adoble/Internet-Radio-Module/hardware/electronics/irm_pcb/irm_pcb.kicad_pcb

## KiCad design hardware/electronics/irm_pcb/irm_pcb.kicad_pcb (2019-12-27)

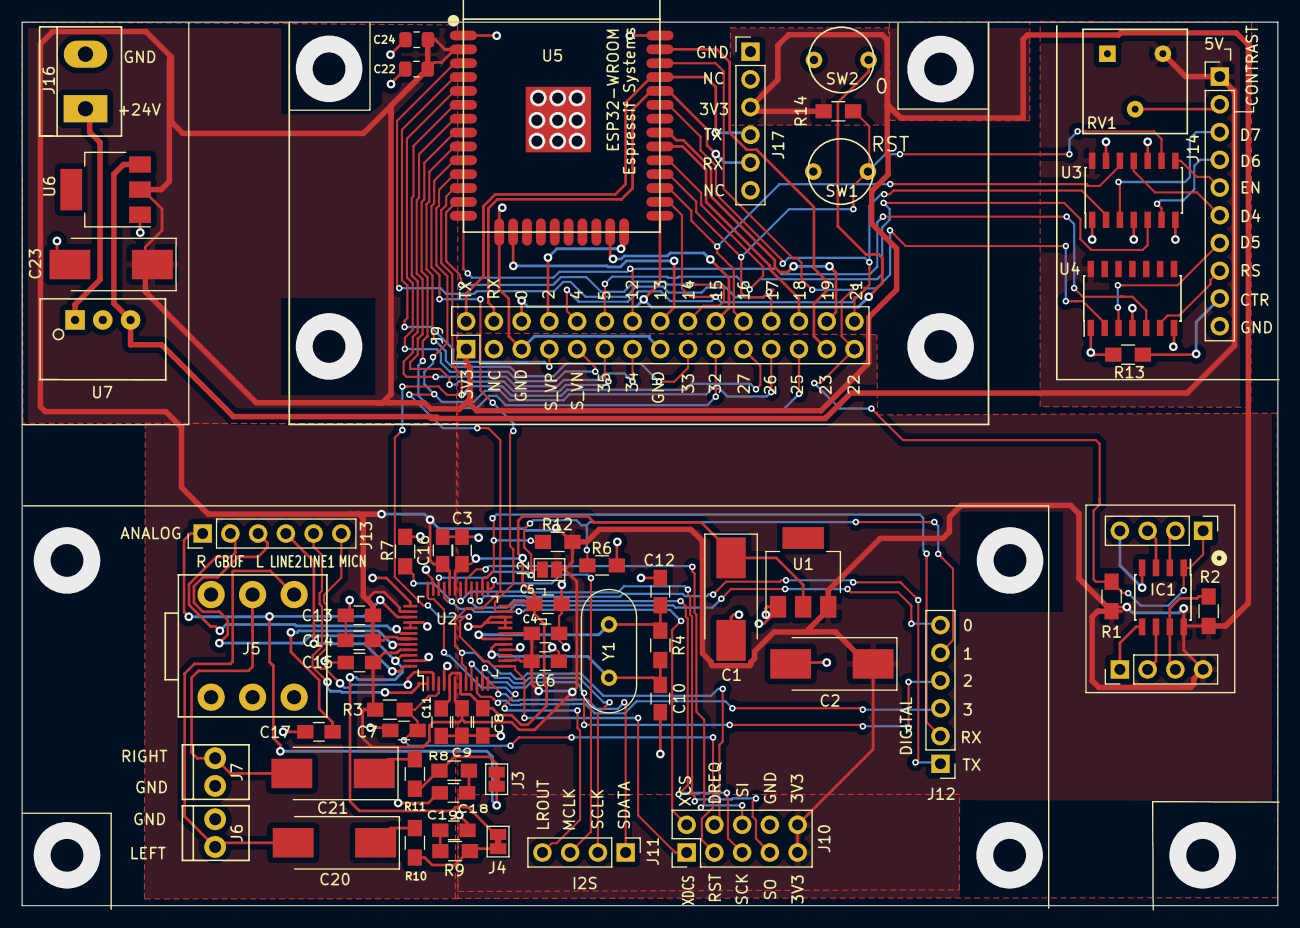
[picture p3: board irm_pcb.kicad_pcb from above]

Board: 2 copper layers, 115.0 x 80.9 mm, 65 parts (0 on the bottom side), 75 nets.

Parts:
C1, C2, C23: 10u; CP_Tantalum_Case-D_EIA-7343-31_Hand
C3, C4, C5, C6, C7, C8, C9, C11, C14, C15, C16: 100n; C_0805_HandSoldering
C10, C12: 22p; C_0805_HandSoldering
C13: 10u; C_0805_HandSoldering
C17: 1u; C_0805_HandSoldering
C18, C19: 10n; C_0805_HandSoldering
C20, C21: 220u; CP_Tantalum_Case-D_EIA-7343-31_Hand
C22: 10u; C_0805_2012Metric_Pad1.15x1.40mm_HandSolder
C24: 100n; C_0805_2012Metric_Pad1.15x1.40mm_HandSolder
IC1: 23LC1024; SOIC-8_3.9x4.9mm_Pitch1.27mm
J1, J8, J11: Conn_01x04; Pin_Header_Straight_1x04_Pitch2.54mm
J2: JUMPER_OPEN; SolderJumper-2_P1.3mm_Open_Pad1.0x1.5mm
J3, J4: JUMPER_CLOSED; SolderJumper-2_P1.3mm_Bridged_Pad1.0x1.5mm
J5: AudioJack3_Switch; Stereo_Jack-Socket_6_Pin
J6, J7: Screw_Terminal_1x02
J9: Conn_02x15_Top_Bottom; Pin_Header_Straight_2x15_Pitch2.54mm
J10: Conn_02x05_Counter_Clockwise; Pin_Header_Straight_2x05_Pitch2.54mm_CC
J12, J13, J17: Conn_01x06; Pin_Header_Straight_1x06_Pitch2.54mm
J14: Conn_01x10; Pin_Header_Straight_1x10_Pitch2.54mm
J16: Screw_Terminal_01x02; Screw_Terminal_1x02_Pitch5.00mm
R1, R2, R13, R14: 10K; R_0805_HandSoldering
R3, R6, R7: 100K; R_0805_HandSoldering
R4: 1M; R_0805_HandSoldering
R8, R9: 22; R_0805_HandSoldering
R10, R11: 100; R_0805_HandSoldering
R12: 100k; R_0805_HandSoldering
RV1: 10K; Potentiometer_Trimmer_Bourns_3386F
SW1: RST; SW-PUSH-RND-SMALL
SW2: 0; SW-PUSH-RND-SMALL
U1: LM1117-1.8; SOT-223
U2: VS1053B; LQFP-48_7x7mm_Pitch0.5mm
U3, U4: 74LS125; SOIC-14_3.9x8.7mm_Pitch1.27mm
U5: ESP32-WROOM-32; ESP32-WROOM-32-Espressif-Symbol-Kicad-62379
U6: LM1117-3.3; SOT-223
U7: TSR1-2450; TSR1-24_TO-220-3_V
Y1: 12.288MHz; Crystal_HC49-U_Vertical

Connections:
+1.8V: C1.1, C3.1, C5.1, C8.1, C11.1, U1.2, U2.5, U2.7, U2.24, U2.31
+3V3: C2.1, C4.1, C6.1, C9.1, C13.1, C14.1, C15.1, C16.1, C22.1, C23.1, C24.1, IC1.8, J2.1, J8.4, J9.1, J10.5, J10.6, J17.3, R1.1, R2.1, R3.2, R12.1, R14.1, U1.3, U2.6, U2.14, U2.19, U2.32, U2.38, U2.43, U2.45, U5.2, U6.2
+5V: J14.1, RV1.3, U3.14, U4.14, U6.3, U7.3
+24V: J16.1, U7.1
/Buffer RAM/RAM-CS: IC1.1, J1.1, J9.15, R1.2, U5.36
/Buffer RAM/SCK: IC1.6, J8.2
/Buffer RAM/SI: IC1.5, J8.1
/Buffer RAM/SIO2: IC1.3, J1.3
/Buffer RAM/SO: IC1.2, J1.2
/Buffer RAM/~HOLD/~SIO3: IC1.7, J8.3, R2.2
/Control/CONTRAST: J14.2, RV1.2
/Control/CONTROL: J14.9, R13.1
/Control/D4: J9.26, U3.12, U5.27
/Control/D4_EXT: J14.6, U3.11
/Control/D5: J9.20, U4.2, U5.26
/Control/D5_EXT: J14.7, U4.3
/Control/D6: J9.21, U3.5, U5.29
/Control/D6_EXT: J14.4, U3.6
/Control/D7: J9.30, U3.2, U5.33
/Control/D7_EXT: J14.3, U3.3
/Control/EN: J9.27, R14.2, SW1.1, U3.9, U5.3, U5.28
/Control/EN_EXT: J14.5, U3.8
/Control/RS: J9.22, U4.5, U5.14
/Control/RS_EXT: J14.8, U4.6
/MP3 Codec/DREQ: J9.12, J10.9, U2.8, U5.11
/MP3 Codec/GBUF: J13.2, U2.42
/MP3 Codec/GPIO0: J12.6, R7.2, U2.33
/MP3 Codec/GPIO1: J2.2, J12.5, R6.2, U2.34
/MP3 Codec/GPIO2: J12.4, U2.9
/MP3 Codec/GPIO3: J12.3, U2.10
/MP3 Codec/LEFT: J4.1, J13.3, U2.46
/MP3 Codec/LINE2: J13.4, U2.48
/MP3 Codec/LROUT/GPIO4: J11.4, U2.36
/MP3 Codec/L_OUT: C20.2, J5.T, J6.2
/MP3 Codec/MCLK/GPIO5: J11.3, U2.25
/MP3 Codec/MICN: J13.6, U2.2
/MP3 Codec/MICP/LINE1: J13.5, U2.1
/MP3 Codec/MP3RST: C7.1, J10.2, R3.1, U2.3
/MP3 Codec/RIGHT: J3.1, J13.1, U2.39
/MP3 Codec/RX: J12.2, R12.2, U2.26
/MP3 Codec/R_OUT: C21.2, J5.R, J7.1
/MP3 Codec/SCK: J10.3, U2.28
/MP3 Codec/SCLK/GPIO6: J11.2, U2.11
/MP3 Codec/SDATA/GPIO7: J11.1, U2.12
/MP3 Codec/SI: J10.8, U2.29
/MP3 Codec/SO: J10.4, U2.30
/MP3 Codec/TX: J12.1, U2.27
/MP3 Codec/XCS: J9.13, J10.10, U2.23, U5.10
/MP3 Codec/XDCS: J9.11, J10.1, U2.13, U5.12
/WROOM Processor/IO0: J9.18, SW2.1, U5.25
/WROOM Processor/IO2: J9.19, U5.24
/WROOM Processor/IO13: J9.23, U5.16
/WROOM Processor/IO14: J9.24, U5.13
/WROOM Processor/IO15: J9.25, U5.23
/WROOM Processor/IO32: J9.10, U5.8
/WROOM Processor/IO33: J9.9, U5.9
/WROOM Processor/IO34: J9.7, U5.6
/WROOM Processor/IO35: J9.6, U5.7
/WROOM Processor/RXDO: J9.17, J17.5, U5.34
/WROOM Processor/SCK: J9.28, U5.30
/WROOM Processor/SENSOR_VN: J9.5, U5.5
/WROOM Processor/SENSOR_VP: J9.4, U5.4
/WROOM Processor/SI: J9.14, U5.37
/WROOM Processor/SO: J9.29, U5.31
/WROOM Processor/TXD0: J9.16, J17.4, U5.35
AGND: C1.2, C2.2, C3.2, C4.2, C5.2, C6.2, C7.2, C8.2, C9.2, C10.2, C11.2, C12.2, C13.2, C14.2, C15.2, C16.2, C17.2, C18.2, C19.2, C22.2, C23.2, C24.2, IC1.4, J1.4, J5.S, J6.1, J7.2, J9.3, J9.8, J10.7, J14.10, J16.2, J17.1, R6.1, R7.1, R13.2, RV1.1, SW1.2, SW2.2, U1.1, U2.4, U2.16, U2.20, U2.21, U2.22, U2.35, U2.37, U2.40, U2.41, U2.47, U3.1, U3.4, U3.7, U3.10, U3.13, U4.1, U4.4, U4.7, U5.1, U5.15, U5.38, U5.39, U6.1, U7.2
unnamed: C10.1, R4.2, U2.17, Y1.1
unnamed: C12.1, R4.1, U2.18, Y1.2
unnamed: C17.1, U2.44
unnamed: C18.1, R8.2
unnamed: C19.1, R9.2
unnamed: C20.1, R10.2
unnamed: C21.1, R11.2
unnamed: J3.2, R8.1, R11.1
unnamed: J4.2, R9.1, R10.1
