adoble/Internet-Radio-Module/hardware/electronics/test-rig/test-rig.kicad_pcb

## KiCad design hardware/electronics/test-rig/test-rig.kicad_pcb (2019-11-17)

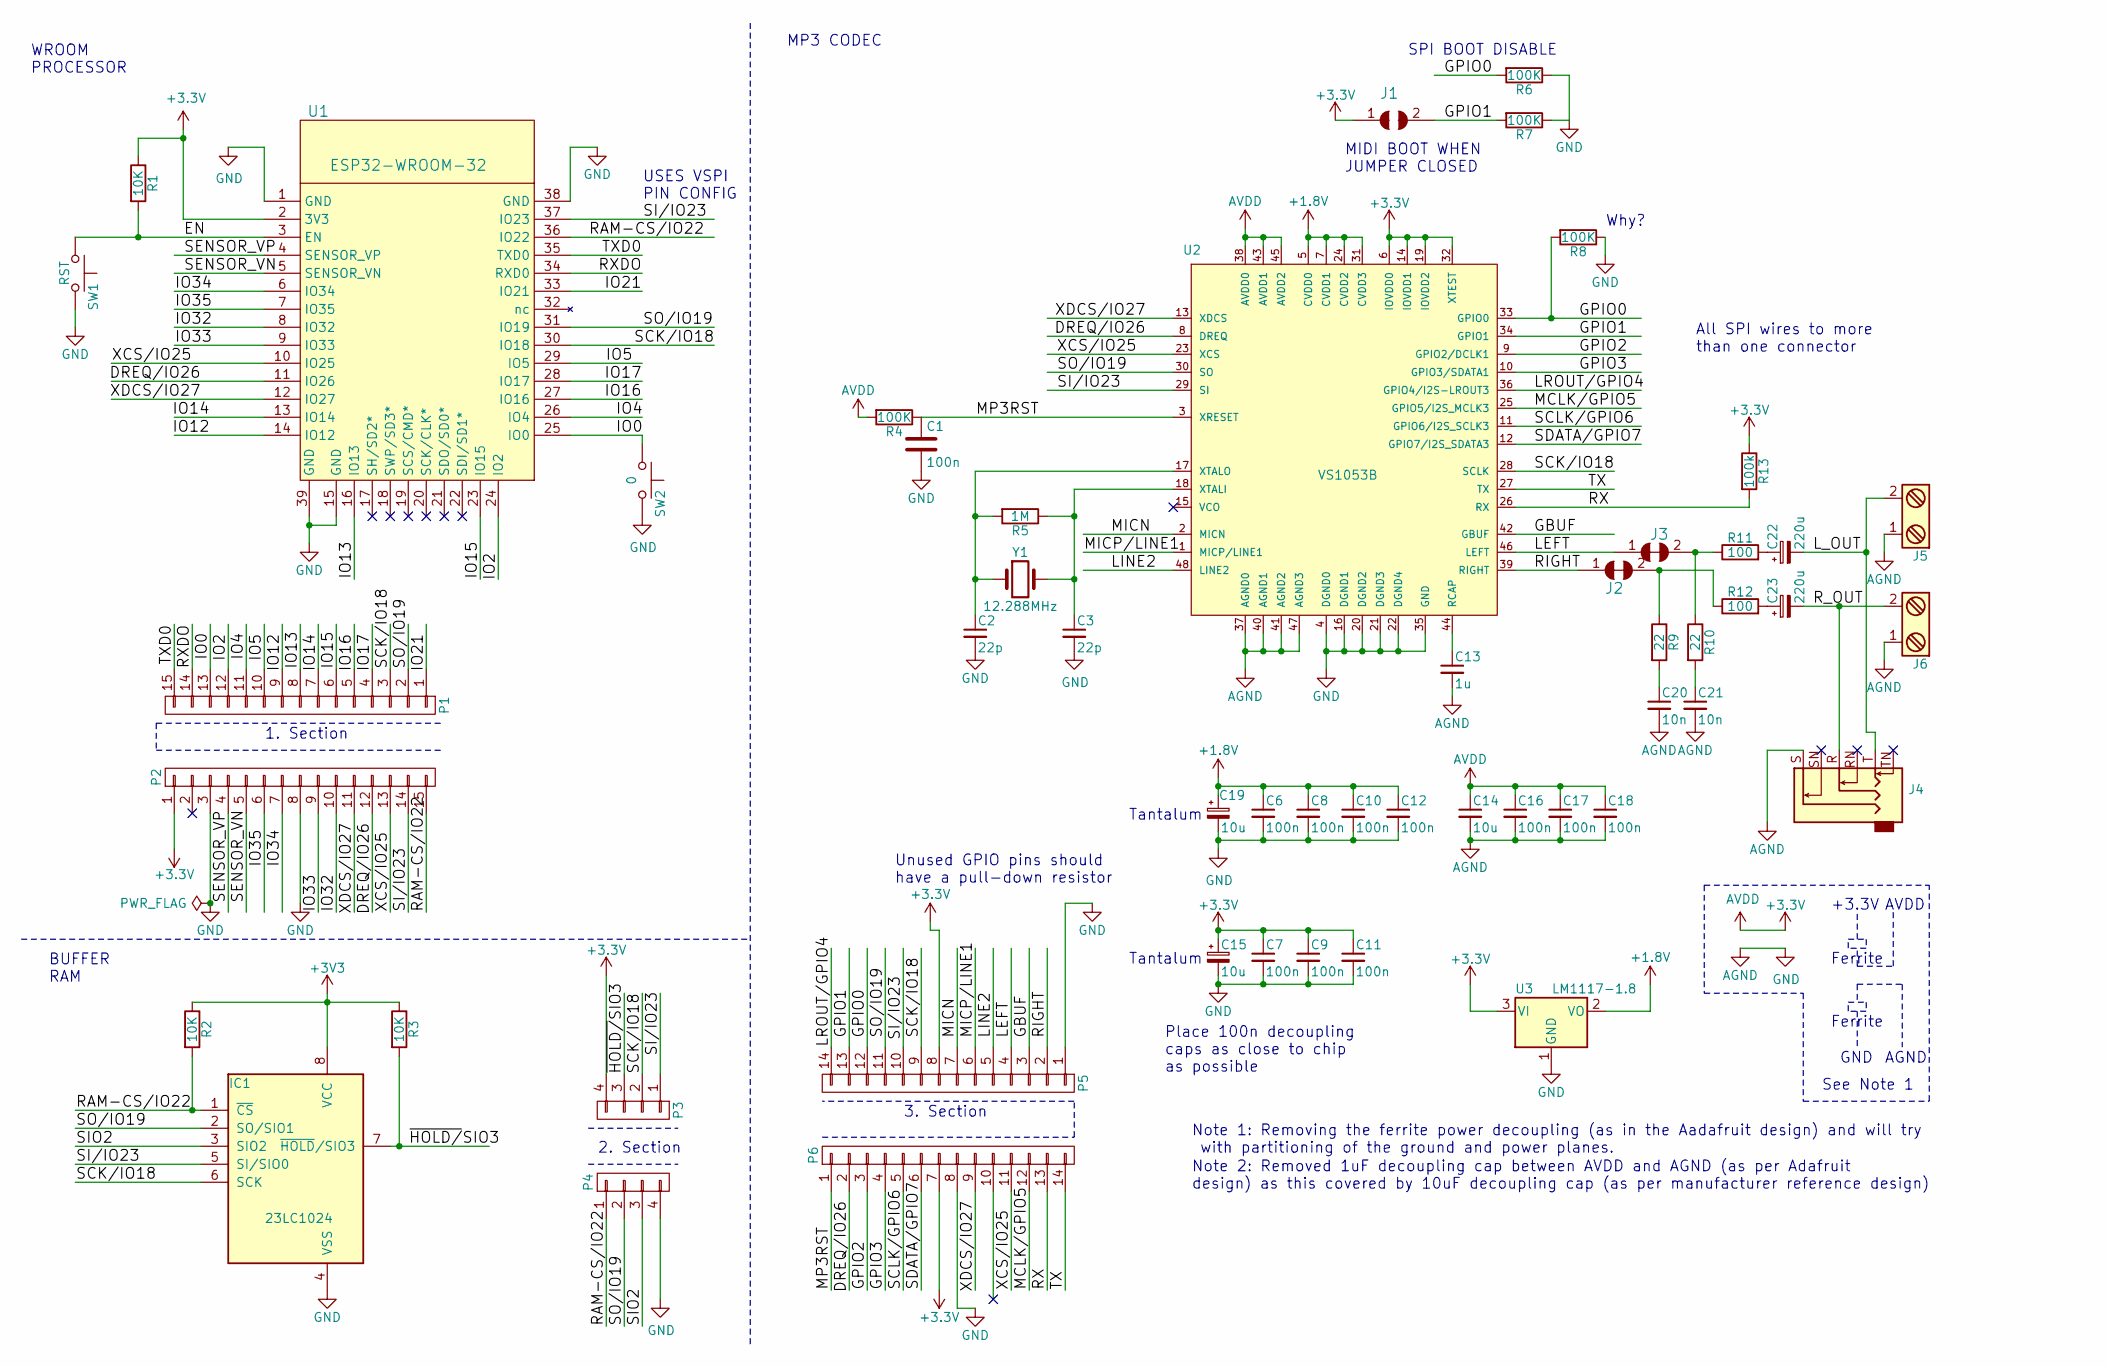
[picture p4: schematic test-rig.sch, Modular Internet Radio Test Rig]

Parts:
C1, C6, C7, C8, C9, C10, C11, C12, C16, C17, C18: 100n; C_0805_HandSoldering
C2, C3: 22p; C_0805_HandSoldering
C13: 1u; C_0805_HandSoldering
C14: 10u; C_0805_HandSoldering
C15, C19: 10u; CP_Tantalum_Case-D_EIA-7343-31_Hand
C20, C21: 10n; C_0805_HandSoldering
C22, C23: 220u; CP_Tantalum_Case-D_EIA-7343-31_Hand
IC1: 23LC1024; SOIC-8_3.9x4.9mm_Pitch1.27mm
J1: JUMPER_OPEN; SolderJumper-2_P1.3mm_Open_Pad1.0x1.5mm
J2, J3: JUMPER_CLOSED; SolderJumper-2_P1.3mm_Bridged_Pad1.0x1.5mm
J4: AudioJack3_Switch; Stereo_Jack-Socket_6_Pin
J5, J6: Screw_Terminal_1x02
P1, P2: CONN_01X15; Pin_Header_Straight_1x15_Pitch2.54mm
P3, P4: CONN_01X04; Pin_Header_Straight_1x04_Pitch2.54mm
P5, P6: CONN_01X14; Pin_Header_Straight_1x14_Pitch2.54mm
R1, R2, R3: 10K; R_0805_HandSoldering
R4, R6, R7, R8: 100K; R_0805_HandSoldering
R5: 1M; R_0805_HandSoldering
R9, R10: 22; R_0805_HandSoldering
R11, R12: 100; R_0805_HandSoldering
R13: 100k; R_0805_HandSoldering
SW1: RST; SW-PUSH-RND-SMALL
SW2: 0; SW-PUSH-RND-SMALL
U1: ESP32-WROOM-32; ESP32-WROOM-32-Espressif-Symbol-Kicad-62379
U2: VS1053B; LQFP-48_7x7mm_Pitch0.5mm
U3: LM1117-1.8; SOT-223
Y1: 12.288MHz; Crystal_HC49-U_Vertical

Connections:
+1.8V: C6.1, C8.1, C10.1, C12.1, C19.1, U2.5 (CVDD0), U2.7 (CVDD1), U2.24 (CVDD2), U2.31 (CVDD3), U3.2 (VO)
/DREQ/IO26: P2.12, P6.2, U1.11 (IO26), U2.8 (DREQ)
/EN: R1.2, SW1.1, U1.3 (EN)
/GBUF: P5.3, U2.42 (GBUF)
/GPIO0: P5.12, R6.2, R8.2, U2.33 (GPIO0)
/GPIO1: J1.2, P5.13, R7.2, U2.34 (GPIO1)
/GPIO2: P6.3, U2.9 (GPIO2/DCLK1)
/GPIO3: P6.4, U2.10 (GPIO3/SDATA1)
/IO0: P1.13, SW2.1, U1.25 (IO0)
/IO2: P1.12, U1.24 (IO2)
/IO4: P1.11, U1.26 (IO4)
/IO5: P1.10, U1.29 (IO5)
/IO12: P1.9, U1.14 (IO12)
/IO13: P1.8, U1.16 (IO13)
/IO14: P1.7, U1.13 (IO14)
/IO15: P1.6, U1.23 (IO15)
/IO16: P1.5, U1.27 (IO16)
/IO17: P1.4, U1.28 (IO17)
/IO21: P1.1, U1.33 (IO21)
/IO32: P2.10, U1.8 (IO32)
/IO33: P2.9, U1.9 (IO33)
/IO34: P2.7, U1.6 (IO34)
/IO35: P2.6, U1.7 (IO35)
/LEFT: J3.1, P5.4, U2.46 (LEFT)
/LINE2: P5.5, U2.48 (LINE2)
/LROUT/GPIO4: P5.14, U2.36 (GPIO4/I2S-LROUT3)
/L_OUT: C22.2, J4.T, J5.2
/MCLK/GPIO5: P6.12, U2.25 (GPIO5/I2S_MCLK3)
/MICN: P5.7, U2.2 (MICN)
/MICP/LINE1: P5.6, U2.1 (MICP/LINE1)
/MP3RST: C1.1, P6.1, R4.1, U2.3 (XRESET)
/RAM-CS/IO22: IC1.1 (~CS), P2.15, P4.1, R2.2, U1.36 (IO22)
/RIGHT: J2.1, P5.2, U2.39 (RIGHT)
/RX: P6.13, R13.2, U2.26 (RX)
/RXDO: P1.14, U1.34 (RXD0)
/R_OUT: C23.2, J4.R, J6.2
/SCK/IO18: IC1.6 (SCK), P1.3, P3.2, P5.9, U1.30 (IO18), U2.28 (SCLK)
/SCLK/GPIO6: P6.5, U2.11 (GPIO6/I2S_SCLK3)
/SDATA/GPIO7: P6.6, U2.12 (GPIO7/I2S_SDATA3)
/SENSOR_VN: P2.5, U1.5 (SENSOR_VN)
/SENSOR_VP: P2.4, U1.4 (SENSOR_VP)
/SI/IO23: IC1.5 (SI/SIO0), P2.14, P3.1, P5.10, U1.37 (IO23), U2.29 (SI)
/SIO2: IC1.3 (SIO2), P4.3
/SO/IO19: IC1.2 (SO/SIO1), P1.2, P4.2, P5.11, U1.31 (IO19), U2.30 (SO)
/TX: P6.14, U2.27 (TX)
/TXD0: P1.15, U1.35 (TXD0)
/XCS/IO25: P2.13, P6.11, U1.10 (IO25), U2.23 (XCS)
/XDCS/IO27: P2.11, P6.9, U1.12 (IO27), U2.13 (XDCS)
/~HOLD/~SIO3: IC1.7 (~HOLD~/SIO3), P3.3, R3.2
AGND: C1.2, C2.2, C3.2, C6.2, C7.2, C8.2, C9.2, C10.2, C11.2, C12.2, C13.2, C14.2, C15.2, C16.2, C17.2, C18.2, C19.2, C20.2, C21.2, IC1.4 (VSS), J4.S, J5.1, J6.1, P2.3, P2.8, P4.4, P5.1, P6.8, R6.1, R7.1, R8.1, SW1.2, SW2.2, U1.1 (GND), U1.15 (GND), U1.38 (GND), U1.39 (GND), U2.4 (DGND0), U2.16 (DGND1), U2.20 (DGND2), U2.21 (DGND3), U2.22 (DGND4), U2.35 (GND), U2.37 (AGND0), U2.40 (AGND1), U2.41 (AGND2), U2.47 (AGND3), U3.1 (GND)
unnamed: C2.1, R5.2, U2.17 (XTALO), Y1.1
unnamed: C3.1, R5.1, U2.18 (XTALI), Y1.2
unnamed: C13.1, U2.44 (RCAP)
unnamed: C20.1, R9.2
unnamed: C21.1, R10.2
unnamed: C22.1, R11.2
unnamed: C23.1, R12.2
unnamed: J2.2, R9.1, R12.1
unnamed: J3.2, R10.1, R11.1

Notes on the sheet:
Why?
All SPI wires to more than one connector
Unused GPIO pins should have a pull-down resistor
Tantalum
SPI BOOT DISABLE
MIDI BOOT WHEN JUMPER CLOSED
1. Section
2. Section
WROOM PROCESSOR
BUFFER RAM
MP3 CODEC
3. Section
USES VSPI PIN CONFIG
Place 100n decoupling caps as close to chip as possible
AVDD
Ferrite
+3.3V
GND
AGND
Note 1: Removing the ferrite power decoupling (as in the Aadafruit design) and will try with partitioning of the ground and power planes.
See Note 1
Note 2: Removed 1uF decoupling cap between AVDD and AGND (as per Adafruit design) as this covered by 10uF decoupling cap (as per manufacturer reference design)

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
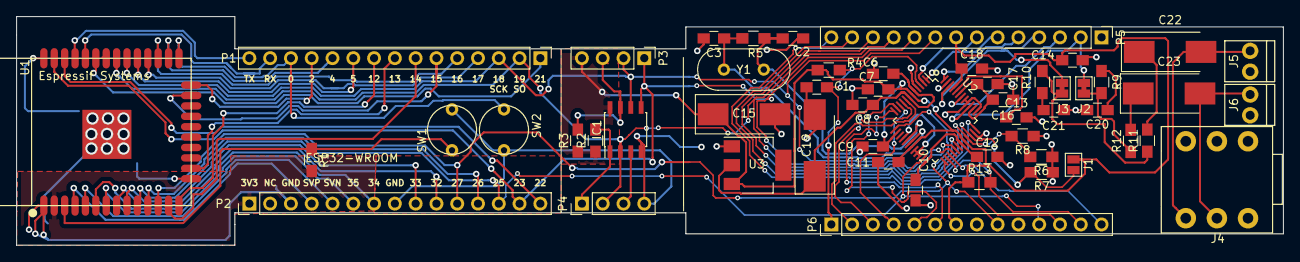
[picture p5: board test-rig.kicad_pcb from above]

Board: 2 copper layers, 154.8 x 27.9 mm, 53 parts (0 on the bottom side), 60 nets.
